Lumethra/keyboard-with-fingerprint-sensor/PCB/Auth75.kicad_sch

## KiCad design PCB/Auth75.kicad_sch (2026-05-24)

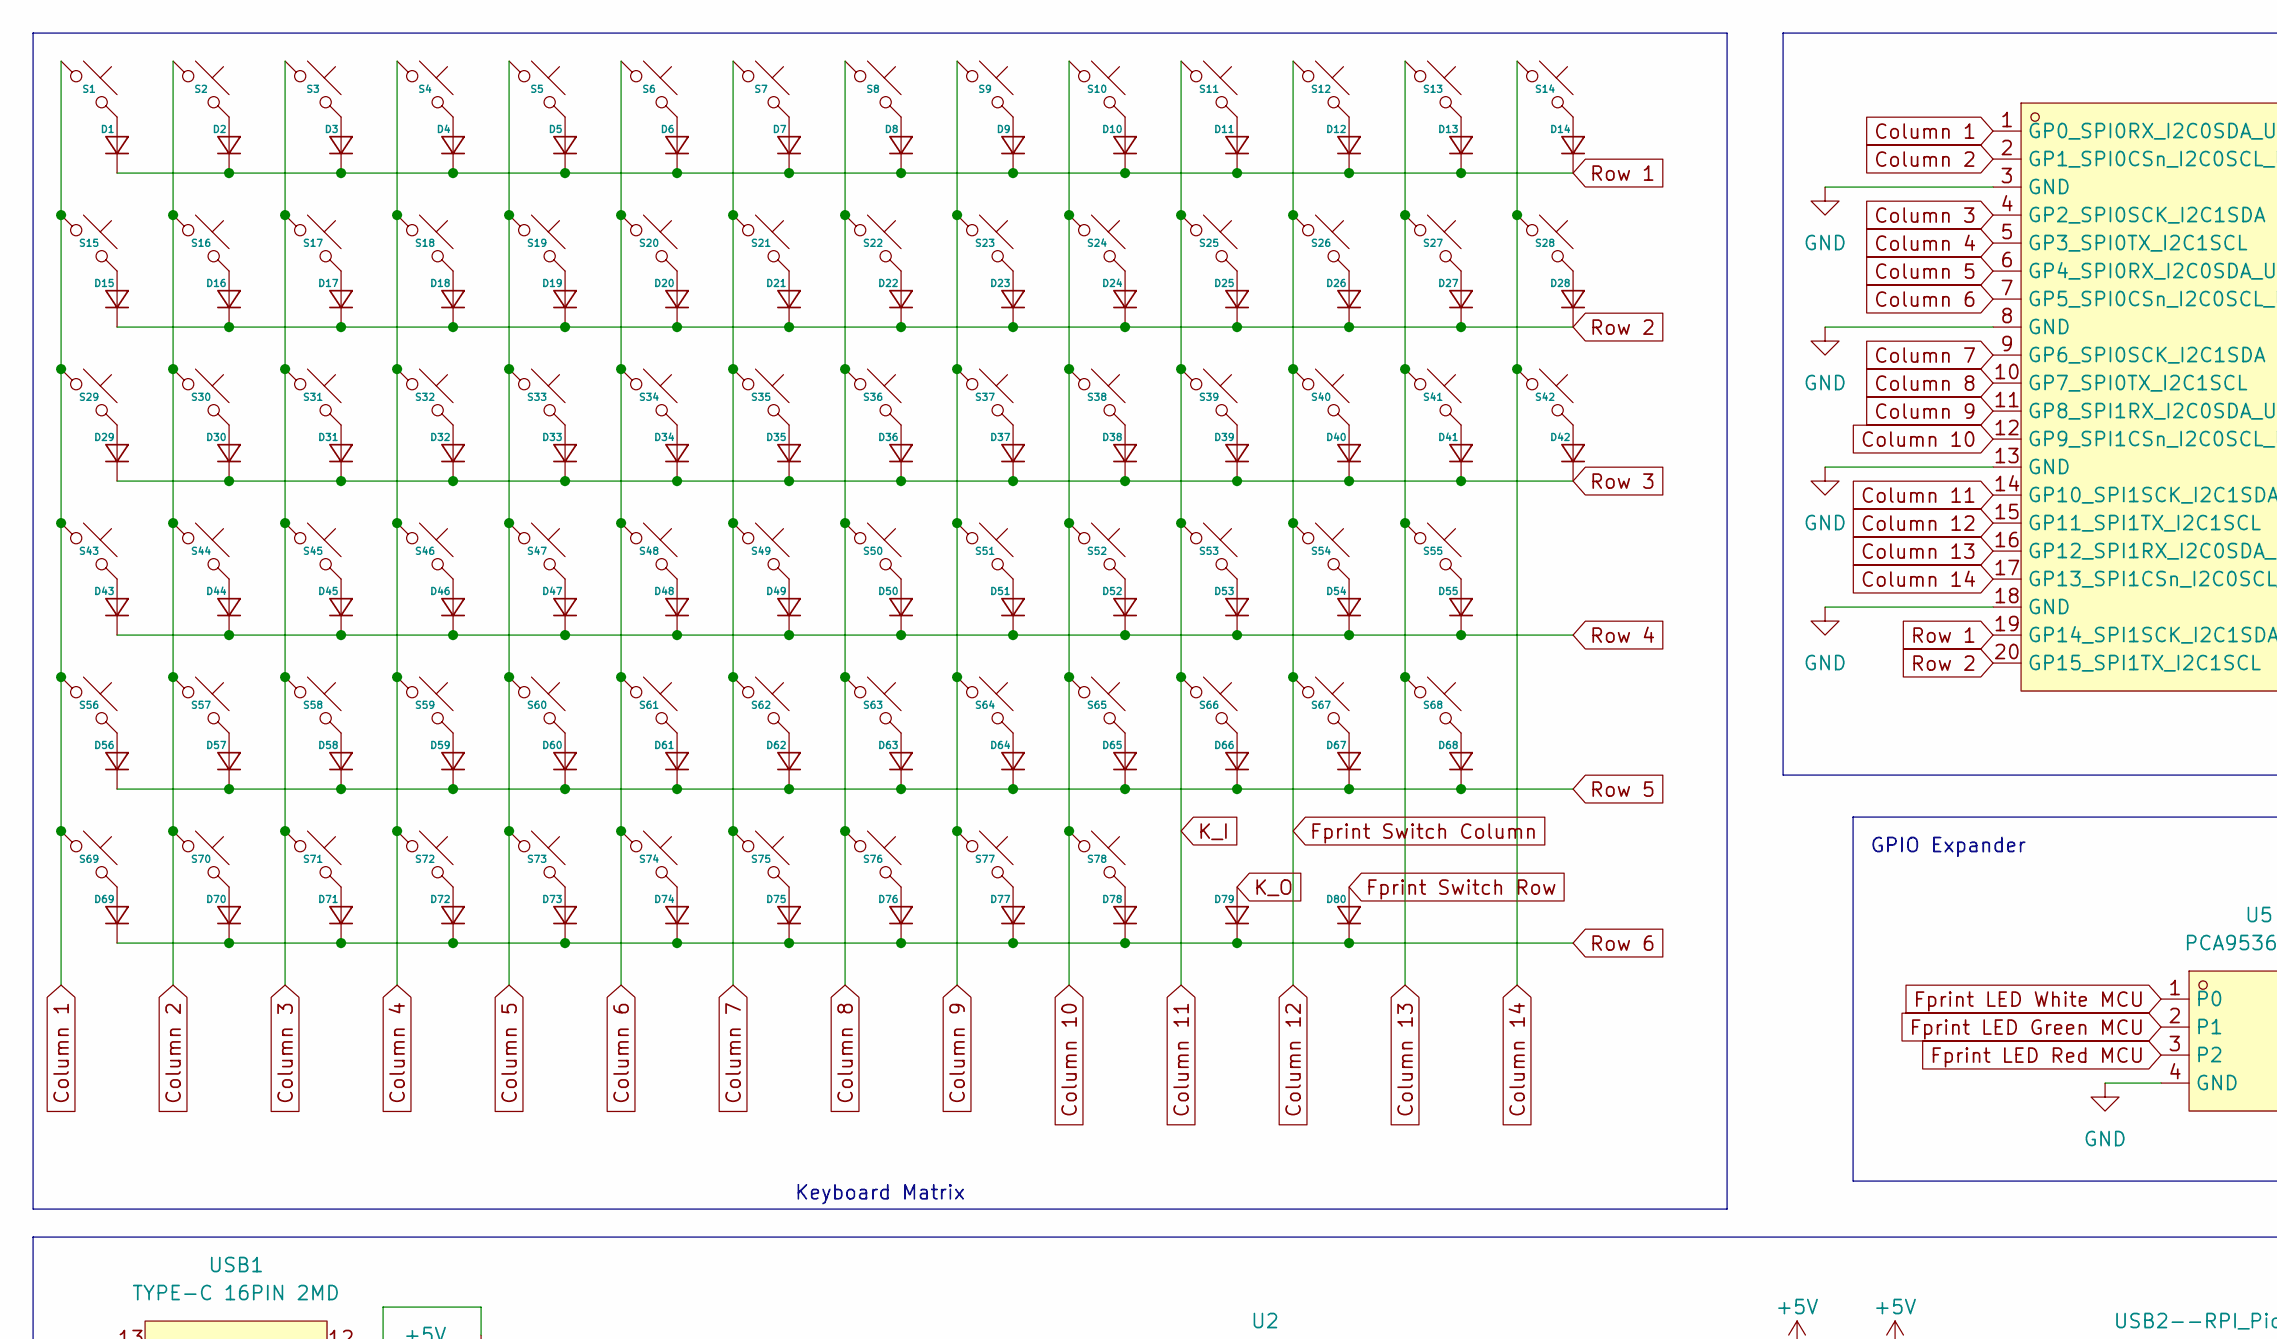
[picture p4: schematic Auth75.kicad_sch, part in row 1, column 1]

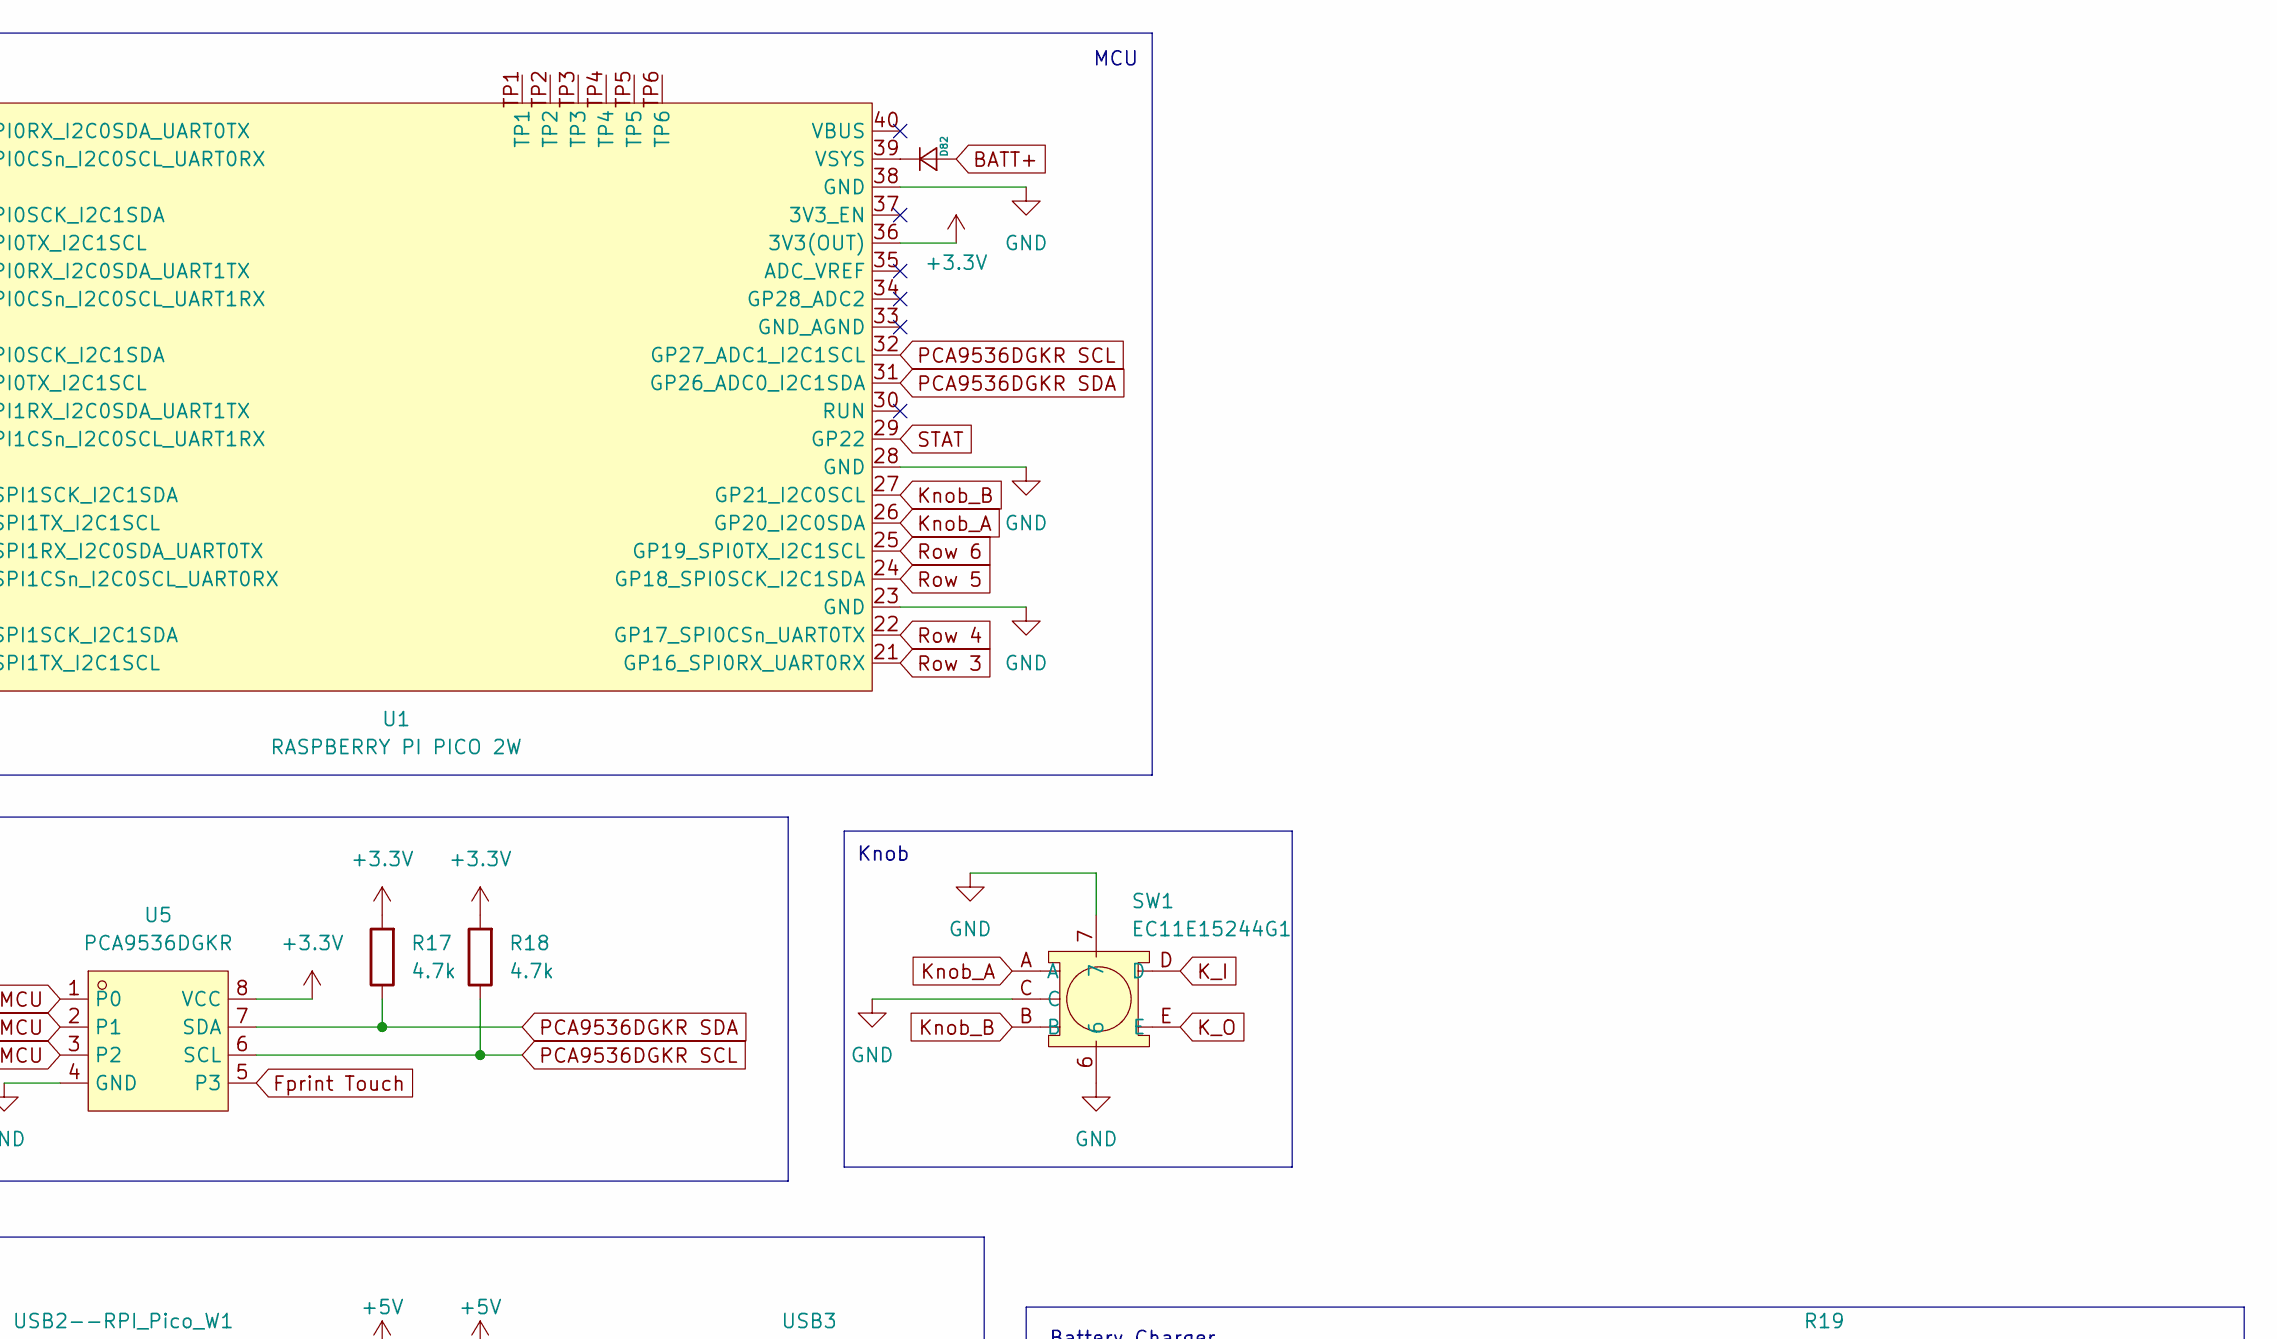
[picture p5: schematic Auth75.kicad_sch, part in row 1, column 2]

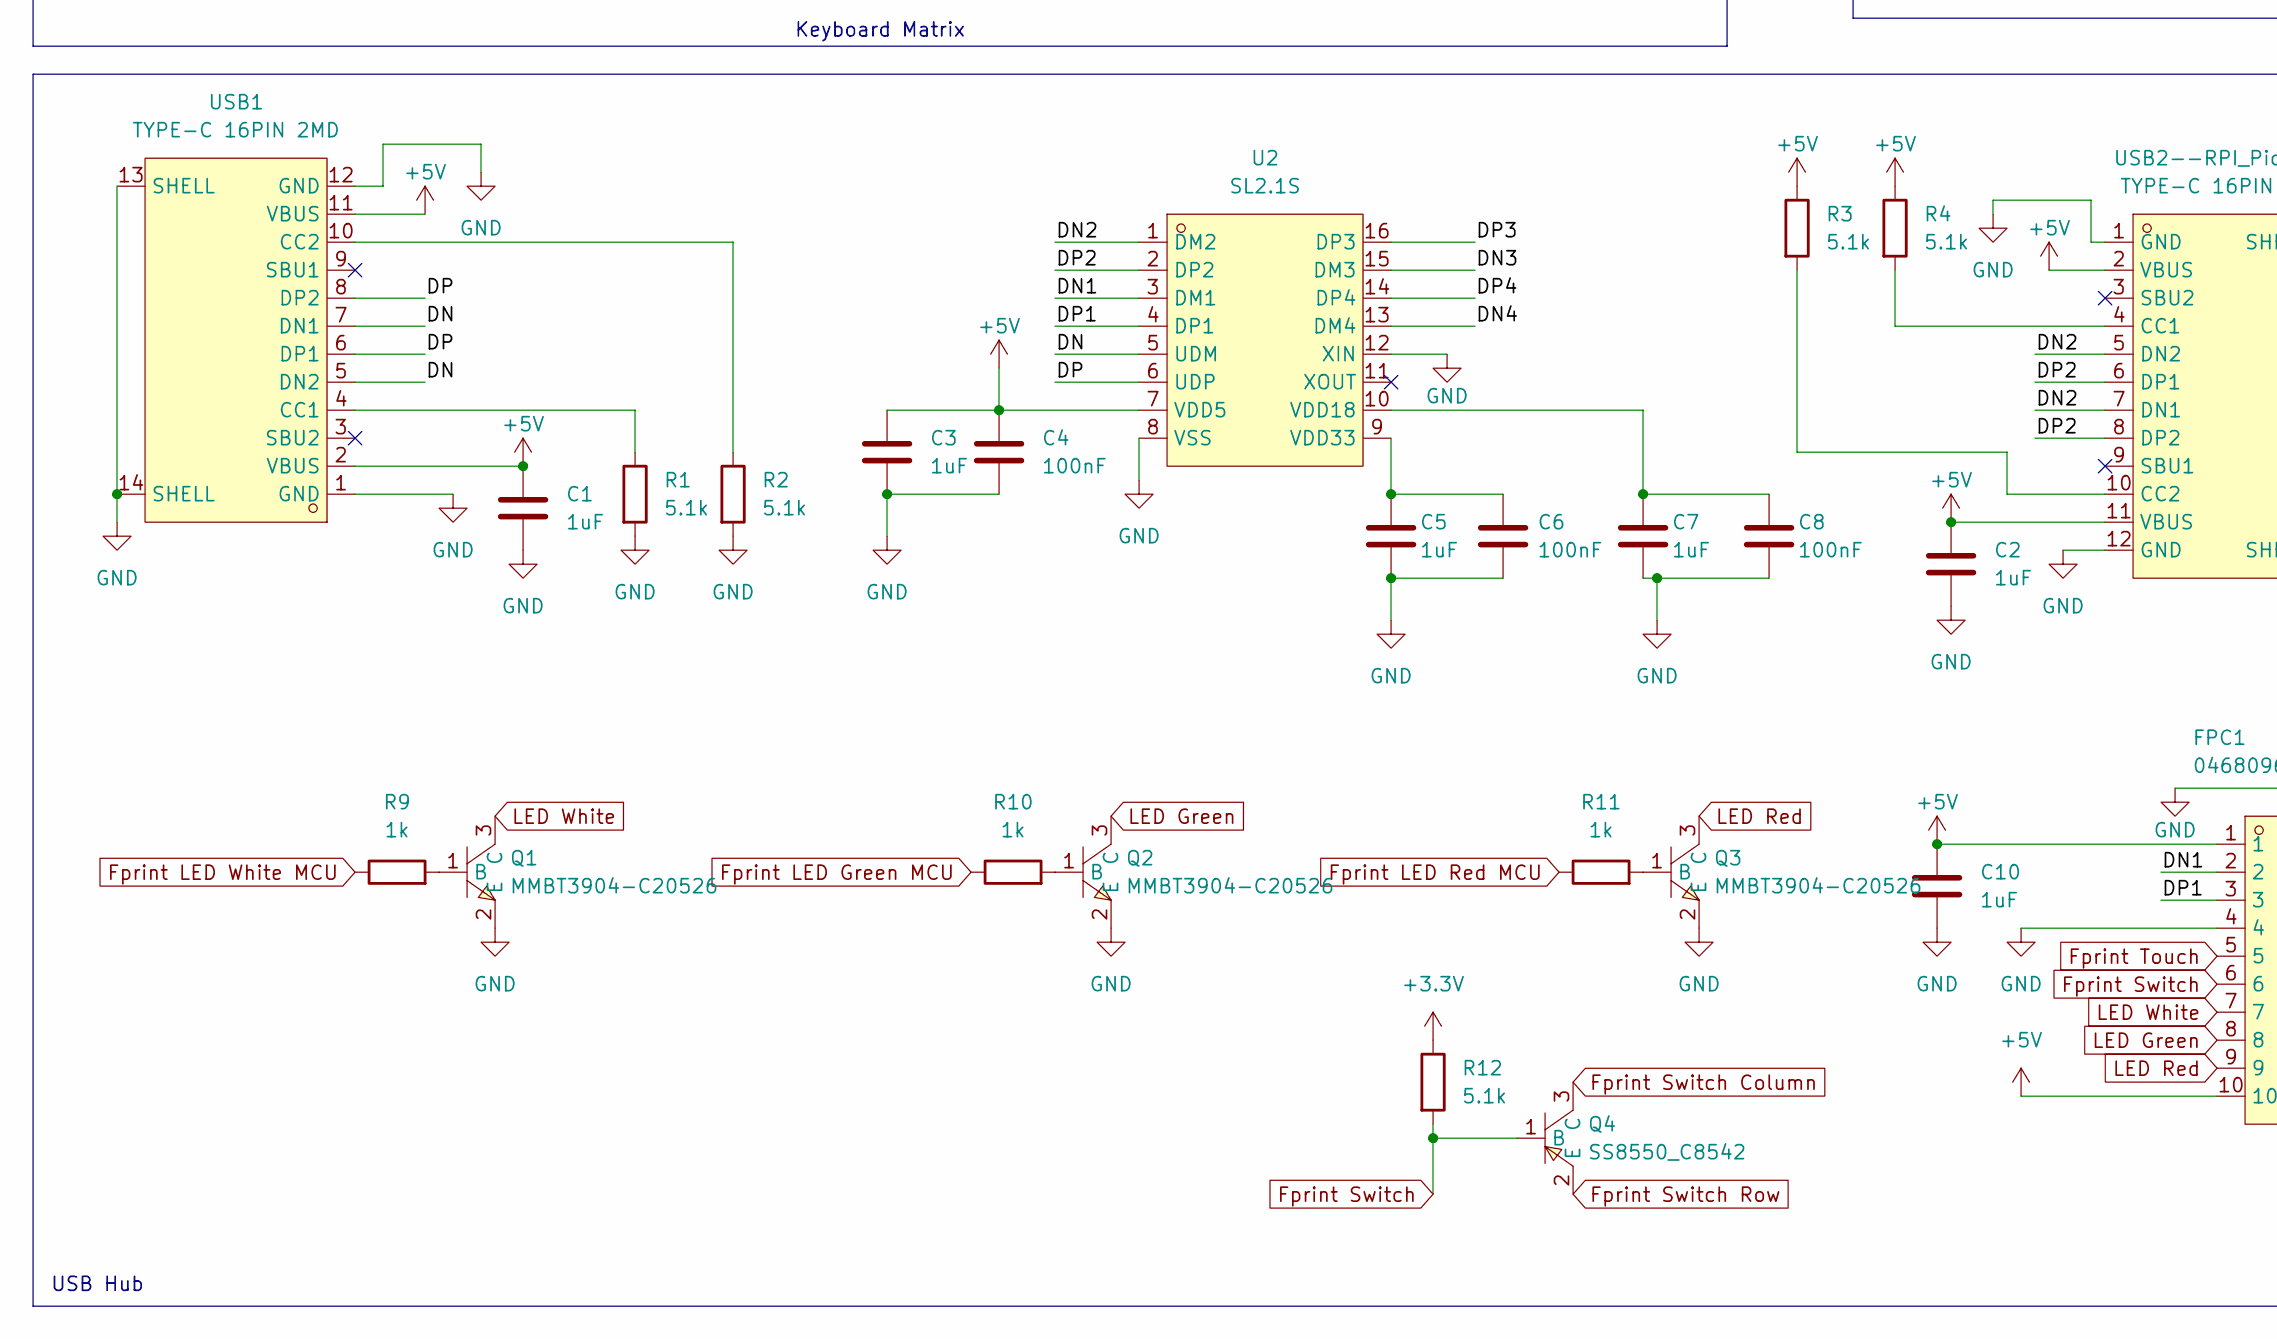
[picture p6: schematic Auth75.kicad_sch, part in row 2, column 1]

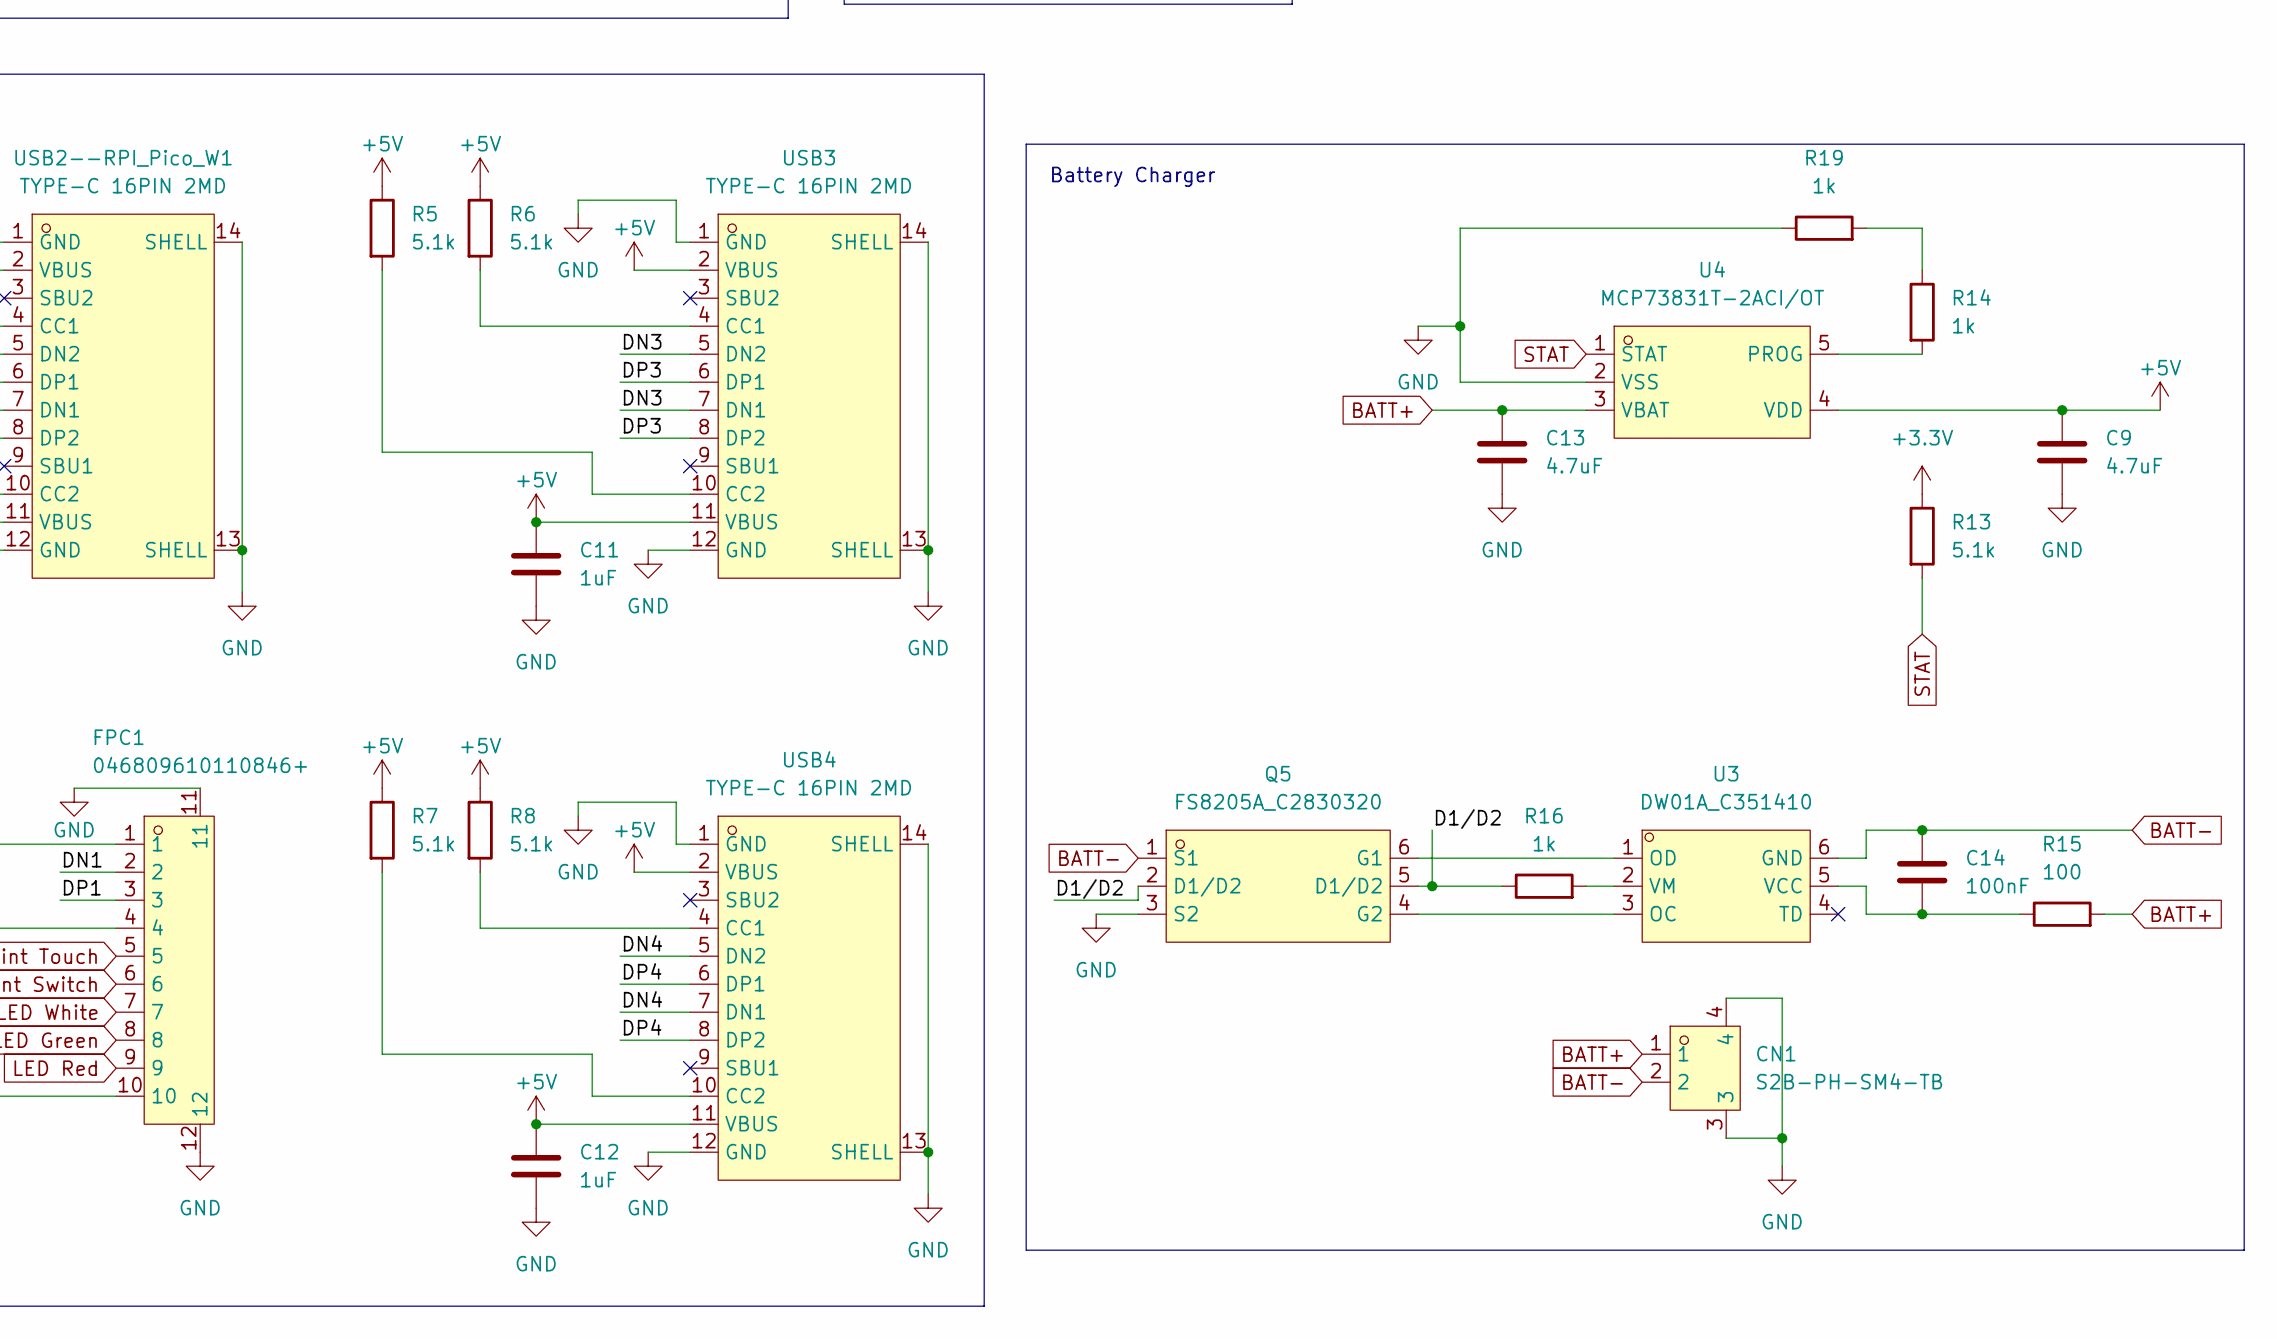
[picture p7: schematic Auth75.kicad_sch, part in row 2, column 2]

Parts:
C1, C2, C3, C5, C7, C10, C11, C12: 1uF; C_0603_1608Metric; LCSC Part C15849
C4, C6, C8, C14: 100nF; C_0603_1608Metric; LCSC Part C14663
C9, C13: 4.7uF; C_0603_1608Metric; LCSC Part C19666
CN1: S2B-PH-SM4-TB; CONN-SMD_P2.00_S2B-PH-SM4-TB-LF-SN; MPN S2B-PH-SM4-TB(LF)(SN); LCSC Part C295747
D1, D2, D3, D4, D5, D6, D7, D8, D9, D10, D11, D12, D13, D14, D15, D16, D17, D18, D19, D20, D21, D22, D23, D24, D25, D26, D27, D28, D29, D30, D31, D32, D33, D34, D35, D36, D37, D38, D39, D40, D41, D42, D43, D44, D45, D46, D47, D48, D49, D50, D51, D52, D53, D54, D55, D56, D57, D58, D59, D60, D61, D62, D63, D64, D65, D66, D67, D68, D69, D70, D71, D72, D73, D74, D75, D76, D77, D78, D79, D80, D82: D_SOD-123; LCSC Part C81598
FPC1: 046809610110846+; CONN-SMD_10P-P0.50_046809610110846; MPN 046809610110846+; LCSC Part C5464531
Q1, Q2, Q3: MMBT3904-C20526; SOT-23-3_L2.9-W1.3-P1.90-LS2.4-BR; MPN MMBT3904(RANGE:100-300); LCSC Part C20526
Q4: SS8550_C8542; SOT-23-3_L2.9-W1.3-P1.90-LS2.4-BR; MPN SS8550 Y2(RANGE:200-350); LCSC Part C8542
Q5: FS8205A_C2830320; SOT-23-6_L2.9-W1.6-P0.95-LS2.8-BR; MPN FS8205A; LCSC Part C2830320
R1, R2, R3, R4, R5, R6, R7, R8, R12, R13: 5.1k; R_0603_1608Metric; LCSC Part C23186
R9, R10, R11, R14, R16, R19: 1k; R_0603_1608Metric; LCSC Part C21190
R15: 100; R_0603_1608Metric; LCSC Part C22775
R17, R18: 4.7k; R_0603_1608Metric; LCSC Part C23162
S1, S2, S3, S4, S5, S6, S7, S8, S9, S10, S11, S12, S13, S14, S15, S16, S17, S18, S19, S20, S21, S22, S23, S24, S25, S26, S27, S28, S29, S30, S31, S32, S33, S34, S35, S36, S37, S38, S39, S40, S41, S42, S43, S44, S45, S46, S47, S48, S49, S50, S51, S52, S53, S54, S55, S56, S57, S58, S59, S60, S61, S62, S63, S64, S65, S66, S67, S68, S69, S70, S71, S72, S73, S74, S75, S76, S77, S78: SW_Hotswap_Kailh_MX; LCSC Part C2803348
SW1: EC11E15244G1; SW-TH_EC11E15244G1; MPN EC11E15244G1; LCSC Part C370970
U1: RASPBERRY PI PICO 2W; COMM-SMD_L51.0-W21.0-P2.54_PICOW; MPN Raspberry Pi Pico 2W; LCSC Part C42394205
U2: SL2.1S; SSOP-16_L4.6-W2.6-P0.53-LS4.0-BL; MPN SL2.1s; LCSC Part C2684433
U3: DW01A_C351410; SOT-23-6_L2.9-W1.6-P0.95-LS2.8-BL; MPN DW01A; LCSC Part C351410
U4: MCP73831T-2ACI/OT; SOT-23-5_L3.0-W1.7-P0.95-LS2.8-BL; MPN MCP73831T-2ACI/OT; LCSC Part C424093
U5: PCA9536DGKR; VSSOP-8_L3.0-W3.0-P0.65-LS4.9-BL; MPN PCA9536DGKR; LCSC Part C2649389
USB1, USB2--RPI_Pico_W1, USB3, USB4: TYPE-C 16PIN 2MD; USB-C-SMD_TYPE-C-6PIN-2MD-073; MPN TYPE-C 16PIN 2MD(073); LCSC Part C2765186

Connections:
+3.3V: R12.1, R13.1, R17.2, R18.2, U1.36 (3V3(OUT)), U5.8 (VCC)
+5V: C1.1, C2.1, C3.1, C4.1, C9.1, C10.1, C11.1, C12.1, FPC1.1, FPC1.10, R3.1, R4.1, R5.1, R6.1, R7.1, R8.1, U2.7 (VDD5), U4.4 (VDD), USB1.2 (VBUS), USB1.11 (VBUS), USB2--RPI_Pico_W1.2 (VBUS), USB2--RPI_Pico_W1.11 (VBUS), USB3.2 (VBUS), USB3.11 (VBUS), USB4.2 (VBUS), USB4.11 (VBUS)
BATT+: C13.1, CN1.1, D82.2 (A), R15.2, U4.3 (VBAT)
BATT-: C14.1, CN1.2, Q5.1 (S1), U3.6 (GND)
Column 1: S1.1, S15.1, S29.1, S43.1, S56.1, S69.1, U1.1 (GP0_SPI0RX_I2C0SDA_UART0TX)
Column 2: S2.1, S16.1, S30.1, S44.1, S57.1, S70.1, U1.2 (GP1_SPI0CSn_I2C0SCL_UART0RX)
Column 3: S3.1, S17.1, S31.1, S45.1, S58.1, S71.1, U1.4 (GP2_SPI0SCK_I2C1SDA)
Column 4: S4.1, S18.1, S32.1, S46.1, S59.1, S72.1, U1.5 (GP3_SPI0TX_I2C1SCL)
Column 5: S5.1, S19.1, S33.1, S47.1, S60.1, S73.1, U1.6 (GP4_SPI0RX_I2C0SDA_UART1TX)
Column 6: S6.1, S20.1, S34.1, S48.1, S61.1, S74.1, U1.7 (GP5_SPI0CSn_I2C0SCL_UART1RX)
Column 7: S7.1, S21.1, S35.1, S49.1, S62.1, S75.1, U1.9 (GP6_SPI0SCK_I2C1SDA)
Column 8: S8.1, S22.1, S36.1, S50.1, S63.1, S76.1, U1.10 (GP7_SPI0TX_I2C1SCL)
Column 9: S9.1, S23.1, S37.1, S51.1, S64.1, S77.1, U1.11 (GP8_SPI1RX_I2C0SDA_UART1TX)
Column 10: S10.1, S24.1, S38.1, S52.1, S65.1, S78.1, U1.12 (GP9_SPI1CSn_I2C0SCL_UART1RX)
Column 11: S11.1, S25.1, S39.1, S53.1, S66.1, SW1.D, U1.14 (GP10_SPI1SCK_I2C1SDA)
Column 12: Q4.3 (C), S12.1, S26.1, S40.1, S54.1, S67.1, U1.15 (GP11_SPI1TX_I2C1SCL)
Column 13: S13.1, S27.1, S41.1, S55.1, S68.1, U1.16 (GP12_SPI1RX_I2C0SDA_UART0TX)
Column 14: S14.1, S28.1, S42.1, U1.17 (GP13_SPI1CSn_I2C0SCL_UART0RX)
D1/D2: Q5.2 (D1/D2), Q5.5 (D1/D2), R16.1
DN: U2.5 (UDM), USB1.5 (DN2), USB1.7 (DN1)
DN1: FPC1.2, U2.3 (DM1)
DN2: U2.1 (DM2), USB2--RPI_Pico_W1.5 (DN2), USB2--RPI_Pico_W1.7 (DN1)
DN3: U2.15 (DM3), USB3.5 (DN2), USB3.7 (DN1)
DN4: U2.13 (DM4), USB4.5 (DN2), USB4.7 (DN1)
DP: U2.6 (UDP), USB1.6 (DP1), USB1.8 (DP2)
DP1: FPC1.3, U2.4 (DP1)
DP2: U2.2 (DP2), USB2--RPI_Pico_W1.6 (DP1), USB2--RPI_Pico_W1.8 (DP2)
DP3: U2.16 (DP3), USB3.6 (DP1), USB3.8 (DP2)
DP4: U2.14 (DP4), USB4.6 (DP1), USB4.8 (DP2)
Fprint LED Green MCU: R10.1, U5.2 (P1)
Fprint LED Red MCU: R11.1, U5.3 (P2)
Fprint LED White MCU: R9.1, U5.1 (P0)
Fprint Switch: FPC1.6, Q4.1 (B), R12.2
Fprint Switch Row: D80.2 (A), Q4.2 (E)
Fprint Touch: FPC1.5, U5.5 (P3)
GND: C1.2, C2.2, C3.2, C4.2, C5.2, C6.2, C7.2, C8.2, C9.2, C10.2, C11.2, C12.2, C13.2, CN1.3, CN1.4, FPC1.4, FPC1.11, FPC1.12, Q1.2 (E), Q2.2 (E), Q3.2 (E), Q5.3 (S2), R1.2, R2.2, R19.1, SW1.6, SW1.7, SW1.C, U1.3 (GND), U1.8 (GND), U1.13 (GND), U1.18 (GND), U1.23 (GND), U1.28 (GND), U1.38 (GND), U2.8 (VSS), U2.12 (XIN), U4.2 (VSS), U5.4 (GND), USB1.1 (GND), USB1.12 (GND), USB1.13 (SHELL), USB1.14 (SHELL), USB2--RPI_Pico_W1.1 (GND), USB2--RPI_Pico_W1.12 (GND), USB2--RPI_Pico_W1.13 (SHELL), USB2--RPI_Pico_W1.14 (SHELL), USB3.1 (GND), USB3.12 (GND), USB3.13 (SHELL), USB3.14 (SHELL), USB4.1 (GND), USB4.12 (GND), USB4.13 (SHELL), USB4.14 (SHELL)
K_O: D79.2 (A), SW1.E
Knob_A: SW1.A, U1.26 (GP20_I2C0SDA)
Knob_B: SW1.B, U1.27 (GP21_I2C0SCL)
LED Green: FPC1.8, Q2.3 (C)
LED Red: FPC1.9, Q3.3 (C)
LED White: FPC1.7, Q1.3 (C)
unnamed: C5.1, C6.1, U2.9 (VDD33)
unnamed: C7.1, C8.1, U2.10 (VDD18)
unnamed: C14.2, R15.1, U3.5 (VCC)
unnamed: D1.2 (A), S1.2
unnamed: D2.2 (A), S2.2
unnamed: D3.2 (A), S3.2
unnamed: D4.2 (A), S4.2
unnamed: D5.2 (A), S5.2
unnamed: D6.2 (A), S6.2
unnamed: D7.2 (A), S7.2
unnamed: D8.2 (A), S8.2
unnamed: D9.2 (A), S9.2
unnamed: D10.2 (A), S10.2
unnamed: D11.2 (A), S11.2
unnamed: D12.2 (A), S12.2
unnamed: D13.2 (A), S13.2
unnamed: D14.2 (A), S14.2
unnamed: D15.2 (A), S15.2
unnamed: D16.2 (A), S16.2
unnamed: D17.2 (A), S17.2
unnamed: D18.2 (A), S18.2
unnamed: D19.2 (A), S19.2
unnamed: D20.2 (A), S20.2
unnamed: D21.2 (A), S21.2
unnamed: D22.2 (A), S22.2
unnamed: D23.2 (A), S23.2
unnamed: D24.2 (A), S24.2
unnamed: D25.2 (A), S25.2
unnamed: D26.2 (A), S26.2
unnamed: D27.2 (A), S27.2
unnamed: D28.2 (A), S28.2
unnamed: D29.2 (A), S29.2
unnamed: D30.2 (A), S30.2
unnamed: D31.2 (A), S31.2
unnamed: D32.2 (A), S32.2
unnamed: D33.2 (A), S33.2
unnamed: D34.2 (A), S34.2
unnamed: D35.2 (A), S35.2
unnamed: D36.2 (A), S36.2
unnamed: D37.2 (A), S37.2
unnamed: D38.2 (A), S38.2
unnamed: D39.2 (A), S39.2
unnamed: D40.2 (A), S40.2
unnamed: D41.2 (A), S41.2
unnamed: D42.2 (A), S42.2
unnamed: D43.2 (A), S43.2
unnamed: D44.2 (A), S44.2
unnamed: D45.2 (A), S45.2
unnamed: D46.2 (A), S46.2
unnamed: D47.2 (A), S47.2
unnamed: D48.2 (A), S48.2
unnamed: D49.2 (A), S49.2
unnamed: D50.2 (A), S50.2
unnamed: D51.2 (A), S51.2
unnamed: D52.2 (A), S52.2
unnamed: D53.2 (A), S53.2
unnamed: D54.2 (A), S54.2
unnamed: D55.2 (A), S55.2
unnamed: D56.2 (A), S56.2
unnamed: D57.2 (A), S57.2
unnamed: D58.2 (A), S58.2
unnamed: D59.2 (A), S59.2
unnamed: D60.2 (A), S60.2
unnamed: D61.2 (A), S61.2
unnamed: D62.2 (A), S62.2
unnamed: D63.2 (A), S63.2
unnamed: D64.2 (A), S64.2
unnamed: D65.2 (A), S65.2
unnamed: D66.2 (A), S66.2
unnamed: D67.2 (A), S67.2
unnamed: D68.2 (A), S68.2
unnamed: D69.2 (A), S69.2
unnamed: D70.2 (A), S70.2
unnamed: D71.2 (A), S71.2
unnamed: D72.2 (A), S72.2
unnamed: D73.2 (A), S73.2
unnamed: D74.2 (A), S74.2
unnamed: D75.2 (A), S75.2
unnamed: D76.2 (A), S76.2
unnamed: D77.2 (A), S77.2
unnamed: D78.2 (A), S78.2
unnamed: D82.1 (K), U1.39 (VSYS)
unnamed: Q1.1 (B), R9.2
unnamed: Q2.1 (B), R10.2
unnamed: Q3.1 (B), R11.2
unnamed: Q5.4 (G2), U3.3 (OC)
unnamed: Q5.6 (G1), U3.1 (OD)
unnamed: R1.1, USB1.4 (CC1)
unnamed: R2.1, USB1.10 (CC2)
unnamed: R3.2, USB2--RPI_Pico_W1.10 (CC2)
unnamed: R4.2, USB2--RPI_Pico_W1.4 (CC1)
unnamed: R5.2, USB3.10 (CC2)
unnamed: R6.2, USB3.4 (CC1)
unnamed: R7.2, USB4.10 (CC2)
unnamed: R8.2, USB4.4 (CC1)
unnamed: R14.1, R19.2
unnamed: R14.2, U4.5 (PROG)
unnamed: R16.2, U3.2 (VM)
PCA9536DGKR SCL: R18.1, U1.32 (GP27_ADC1_I2C1SCL), U5.6 (SCL)
PCA9536DGKR SDA: R17.1, U1.31 (GP26_ADC0_I2C1SDA), U5.7 (SDA)
Row 1: D1.1 (K), D2.1 (K), D3.1 (K), D4.1 (K), D5.1 (K), D6.1 (K), D7.1 (K), D8.1 (K), D9.1 (K), D10.1 (K), D11.1 (K), D12.1 (K), D13.1 (K), D14.1 (K), U1.19 (GP14_SPI1SCK_I2C1SDA)
Row 2: D15.1 (K), D16.1 (K), D17.1 (K), D18.1 (K), D19.1 (K), D20.1 (K), D21.1 (K), D22.1 (K), D23.1 (K), D24.1 (K), D25.1 (K), D26.1 (K), D27.1 (K), D28.1 (K), U1.20 (GP15_SPI1TX_I2C1SCL)
Row 3: D29.1 (K), D30.1 (K), D31.1 (K), D32.1 (K), D33.1 (K), D34.1 (K), D35.1 (K), D36.1 (K), D37.1 (K), D38.1 (K), D39.1 (K), D40.1 (K), D41.1 (K), D42.1 (K), U1.21 (GP16_SPI0RX_UART0RX)
Row 4: D43.1 (K), D44.1 (K), D45.1 (K), D46.1 (K), D47.1 (K), D48.1 (K), D49.1 (K), D50.1 (K), D51.1 (K), D52.1 (K), D53.1 (K), D54.1 (K), D55.1 (K), U1.22 (GP17_SPI0CSn_UART0TX)
Row 5: D56.1 (K), D57.1 (K), D58.1 (K), D59.1 (K), D60.1 (K), D61.1 (K), D62.1 (K), D63.1 (K), D64.1 (K), D65.1 (K), D66.1 (K), D67.1 (K), D68.1 (K), U1.24 (GP18_SPI0SCK_I2C1SDA)
Row 6: D69.1 (K), D70.1 (K), D71.1 (K), D72.1 (K), D73.1 (K), D74.1 (K), D75.1 (K), D76.1 (K), D77.1 (K), D78.1 (K), D79.1 (K), D80.1 (K), U1.25 (GP19_SPI0TX_I2C1SCL)
STAT: R13.2, U1.29 (GP22), U4.1 (STAT)

Notes on the sheet:
GPIO Expander
MCU
Battery Charger
Knob
USB Hub
Keyboard Matrix
